sensebox/senseBox_Eye/examples/GPIO/led-matrix/led-matrix.ino

#include <Adafruit_NeoPixel.h>
#include <Adafruit_NeoMatrix.h>
#include <Adafruit_GFX.h>

#define IO14 14

#define WIDTH 12
#define HEIGHT 8
Adafruit_NeoMatrix matrix = Adafruit_NeoMatrix(WIDTH, HEIGHT, IO14, NEO_MATRIX_TOP + NEO_MATRIX_LEFT + NEO_MATRIX_ROWS + NEO_MATRIX_ZIGZAG, NEO_GRB + NEO_KHZ800);
const uint16_t bitmap_hat[] = {0x0000, 0x0000, 0x0000, 0x0000, 0x0000, 0x0000, 0x0000, 0x0000, 0x0000, 0x0000, 0x0000, 0x0000, 0x0000, 0x0000, 0x0000, 0xB5B6,
0x0000, 0x0000, 0x29B3, 0x29B3, 0x29B3, 0x0000, 0x0000, 0x0000, 0xB5B6, 0xB5B6, 0xE8E4, 0xB5B6, 0xE54F, 0xE54F, 0x29B3, 0x29B3,
0x29B3, 0x74DA, 0x74DA, 0x74DA, 0xB5B6, 0xB5B6, 0xE8E4, 0xB5B6, 0x0000, 0xE54F, 0x29B3, 0x29B3, 0x29B3, 0x74DA, 0x74DA, 0x74DA,
0xB5B6, 0xB5B6, 0xE8E4, 0xB5B6, 0xE54F, 0xE54F, 0x29B3, 0x29B3, 0x29B3, 0x74DA, 0x0000, 0x0000, 0xB5B6, 0xB5B6, 0xE8E4, 0xB5B6,
0x0000, 0xE54F, 0x29B3, 0x29B3, 0x29B3, 0x74DA, 0x74DA, 0x74DA, 0xB5B6, 0xB5B6, 0xE8E4, 0xB5B6, 0xE54F, 0xE54F, 0x29B3, 0x29B3,
0x29B3, 0x74DA, 0x74DA, 0x74DA, 0x0000, 0x0000, 0x0000, 0xB5B6, 0x0000, 0x0000, 0x29B3, 0x29B3, 0x29B3, 0x0000, 0x0000, 0x0000,};

void setup() {
  matrix.setBrightness(20);
  matrix.setTextWrap(false);
  matrix.begin();
  matrix.drawRGBBitmap(0,0, bitmap_hat, WIDTH, HEIGHT);
  matrix.show();
}

void loop() {
}
