sensebox/senseBox_Eye/examples/WiFi+Bluetooth/wifi-connect/wifi-connect.ino

#include <WiFi.h>

#define WIFI_SSID "{{SSID_PLACEHOLDER}}"
#define WIFI_PASSWORD "{{PASSWORD_PLACEHOLDER}}"

void connectToWiFi() {
  Serial.print("Connecting to ");
  Serial.println(WIFI_SSID);
  WiFi.begin(WIFI_SSID, WIFI_PASSWORD);
  
  while (WiFi.status() != WL_CONNECTED) {
    delay(500);
    Serial.print(".");
  }

  if (WiFi.status() == WL_CONNECTED) {
    Serial.println("\nWiFi connected.");
  } else {
    Serial.println("\nFailed to connect to WiFi.");
  }
}

void setup() {
  Serial.begin(115200);
  delay(1500);
  Serial.println();

  connectToWiFi();
}

void loop() {
  // Reconnect to WiFi if needed
  if (WiFi.status() != WL_CONNECTED) {
    Serial.println("WiFi disconnected. Attempting to reconnect...");
    connectToWiFi();
  }

  // Print signal strength
  Serial.print("WiFi RSSI: ");
  Serial.print(WiFi.RSSI());
  Serial.println(" dBm");
  
  delay(1000); // every second
}
