sensebox/senseBox_Eye/examples/I2C/i2c-scanner/i2c-scanner.ino

// based on https://playground.arduino.cc/Main/I2cScanner/

#include <Wire.h>

#define PIN_QWIIC_SDA 2
#define PIN_QWIIC_SCL 1

void setup()
{
  Wire.begin(PIN_QWIIC_SDA,PIN_QWIIC_SCL);

  Serial.begin(115200);
  while (!Serial);
  Serial.println("\nI2C Scanner");
}


void loop()
{
  byte error, address;
  int nDevices;

  Serial.println("Scanning...");

  nDevices = 0;
  for(address = 1; address < 127; address++ ) 
  {
    Wire.beginTransmission(address);
    error = Wire.endTransmission();

    if (error == 0)
    {
      Serial.print("I2C device found at address 0x");
      if (address<16) 
        Serial.print("0");
      Serial.print(address,HEX);
      Serial.println("  !");

      nDevices++;
    }
    else if (error==4) 
    {
      Serial.print("Unknown error at address 0x");
      if (address<16) 
        Serial.print("0");
      Serial.println(address,HEX);
    }    
  }
  if (nDevices == 0)
    Serial.println("No I2C devices found\n");
  else
    Serial.println("done\n");

  delay(500);           // wait half a second for next scan
}
